L-Finistao/Portifolio/Atividades/PPRE8/mapa-mental.jpg

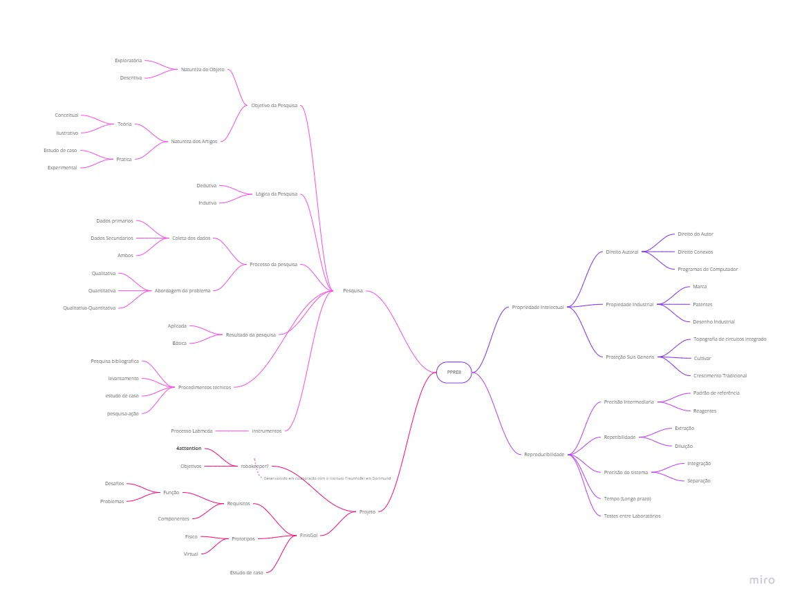
Atividades/PPRE8/mapa-mental.jpg
