L-Finistao/Portifolio/Atividades/PPRE8/Requisitos e Diagramas de Classe UML/Diagrama de Atividade.png

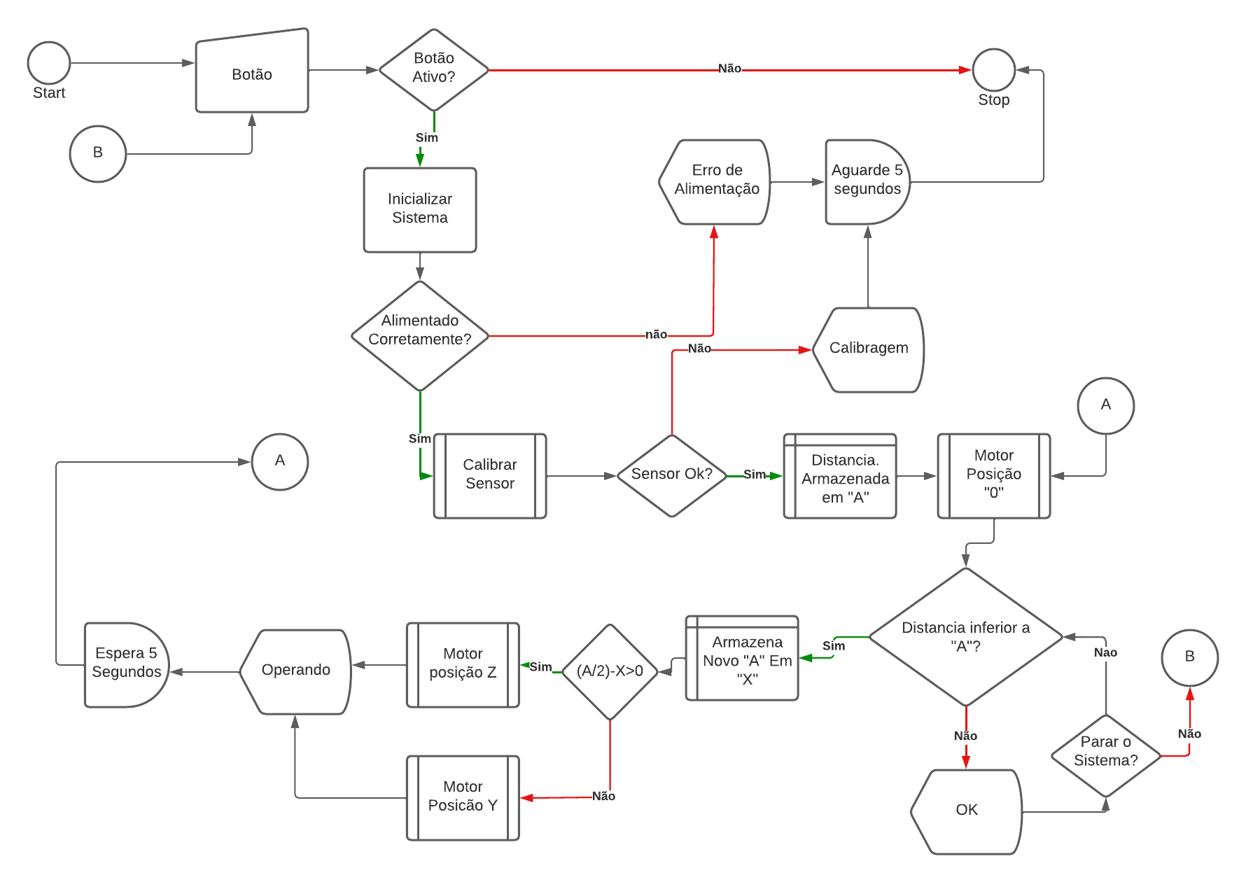
Atividades/PPRE8/Requisitos e Diagramas de Classe UML/Diagrama de Atividade.png
