L-Finistao/Portifolio/Atividades/PPRE8/Requisitos e Diagramas de Classe UML/Diagrama de Estado.png

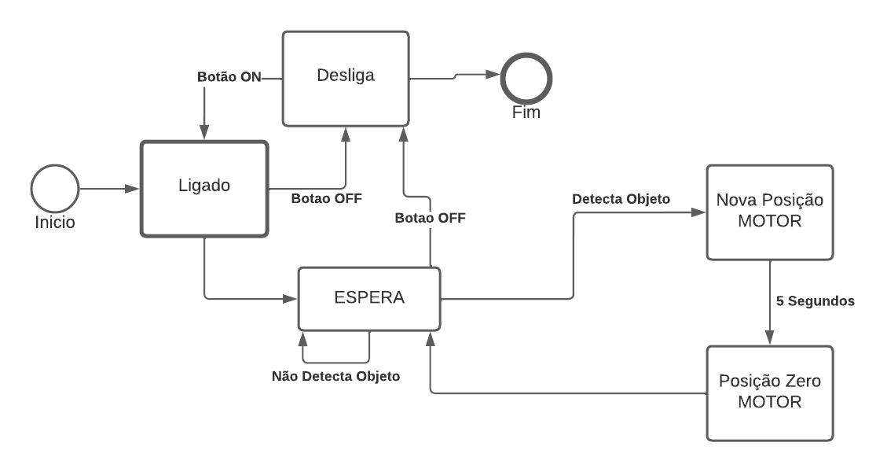
Atividades/PPRE8/Requisitos e Diagramas de Classe UML/Diagrama de Estado.png
