L-Finistao/Portifolio/Projeto/Cronograma definido.PNG

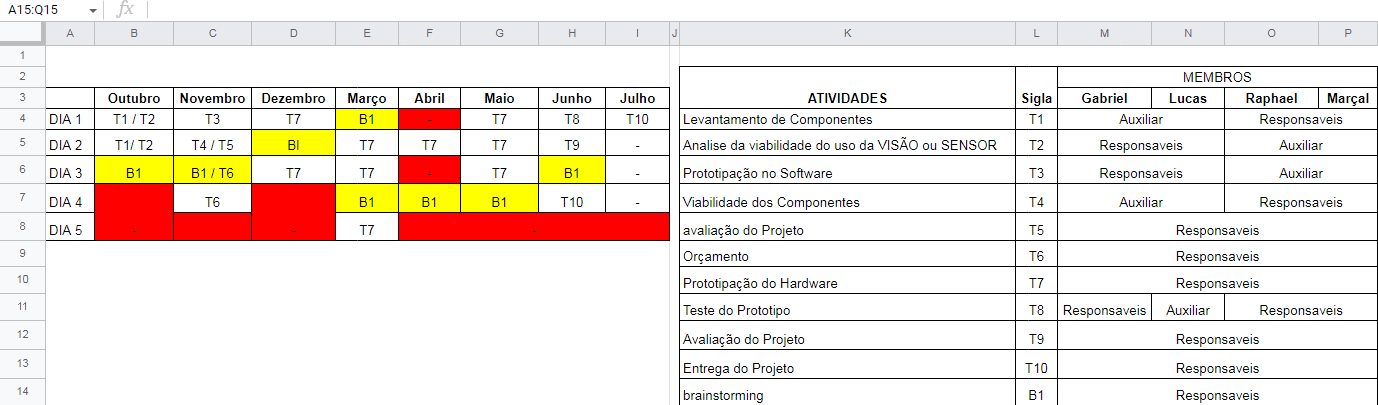
Projeto/Cronograma definido.PNG
