L-Finistao/Portifolio/Projeto/Modelo 3d & Imagens/Imagens e Medidas/Imagens Faces/Base0.jpg

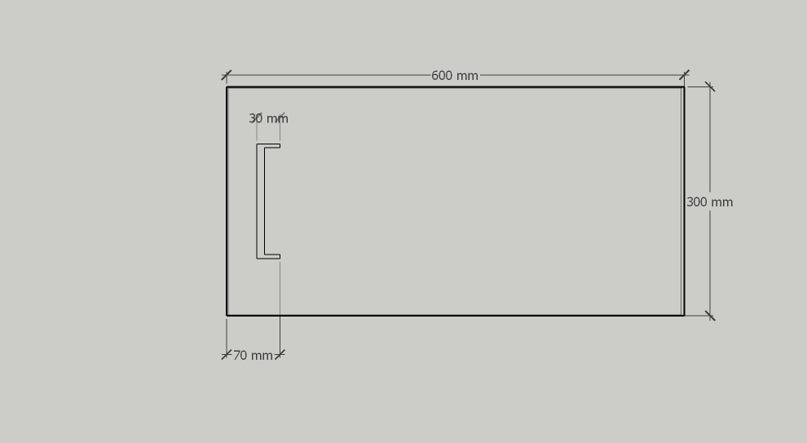
Projeto/Modelo 3d & Imagens/Imagens e Medidas/Imagens Faces/Base0.jpg
