L-Finistao/Portifolio/Projeto/Modelo 3d & Imagens/Imagens e Medidas/Imagens Faces/Eixo.jpg

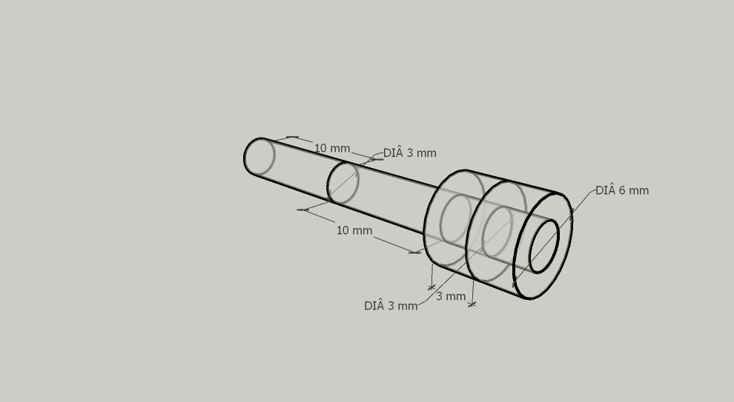
Projeto/Modelo 3d & Imagens/Imagens e Medidas/Imagens Faces/Eixo.jpg
