L-Finistao/Portifolio/Projeto/Modelo 3d & Imagens/Imagens e Medidas/Imagens Faces/Gol.jpg

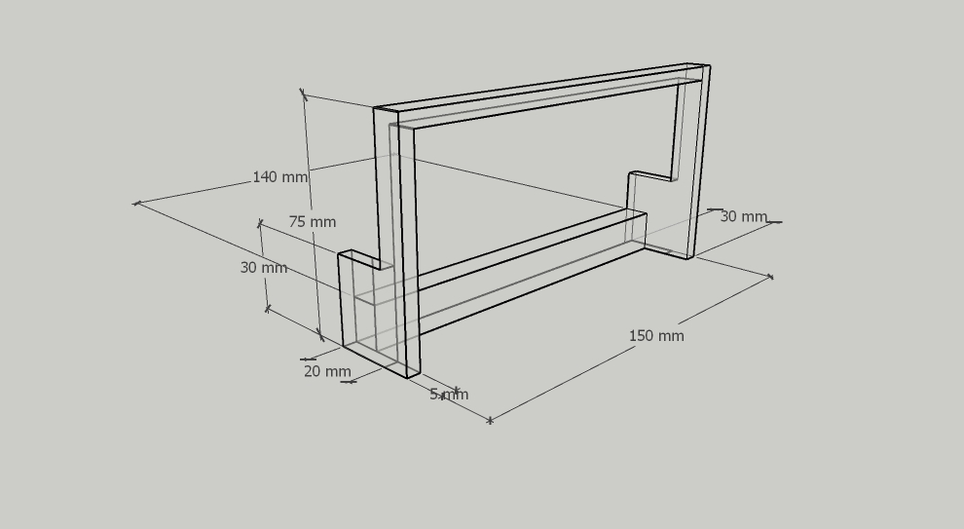
Projeto/Modelo 3d & Imagens/Imagens e Medidas/Imagens Faces/Gol.jpg
