L-Finistao/Portifolio/Projeto/Modelo 3d & Imagens/Imagens e Medidas/Imagens Faces/Suporte1.jpg

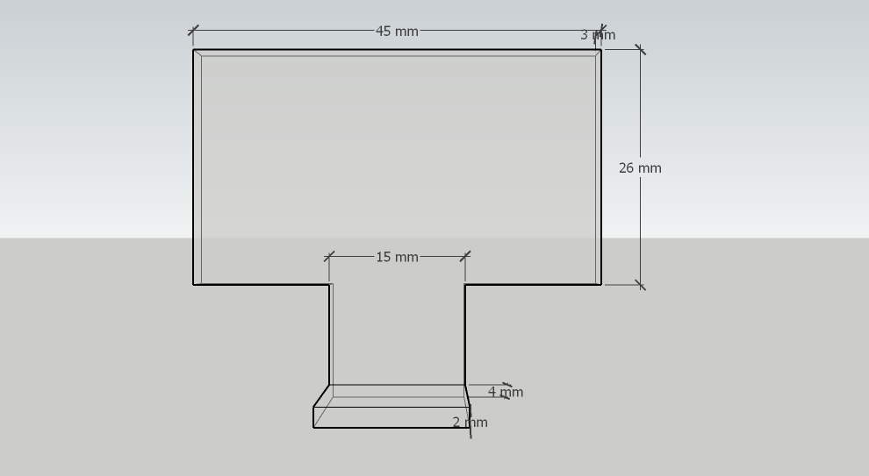
Projeto/Modelo 3d & Imagens/Imagens e Medidas/Imagens Faces/Suporte1.jpg
