L-Finistao/Portifolio/Projeto/Modelo 3d & Imagens/Imagens e Medidas/Imagens Faces/SuporteLed.jpg

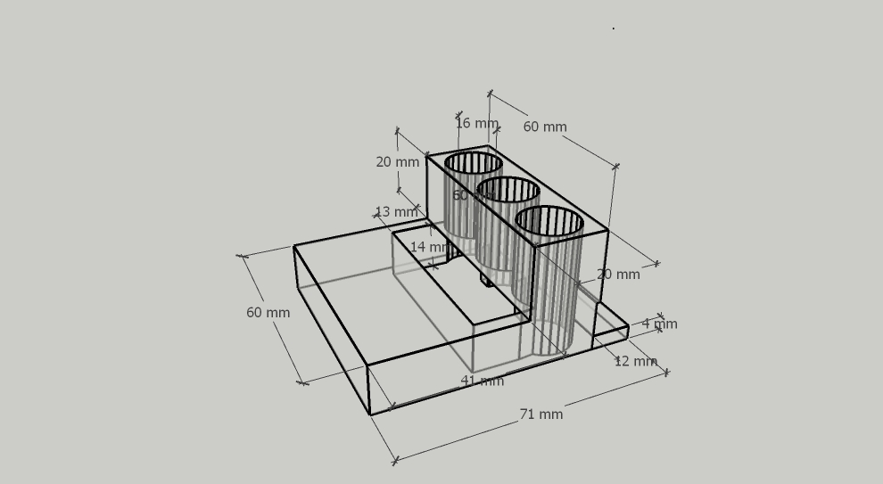
Projeto/Modelo 3d & Imagens/Imagens e Medidas/Imagens Faces/SuporteLed.jpg
