L-Finistao/Portifolio/Projeto/Modelo 3d & Imagens/Imagens e Medidas/Imagens Faces/SuporteMotor.jpg

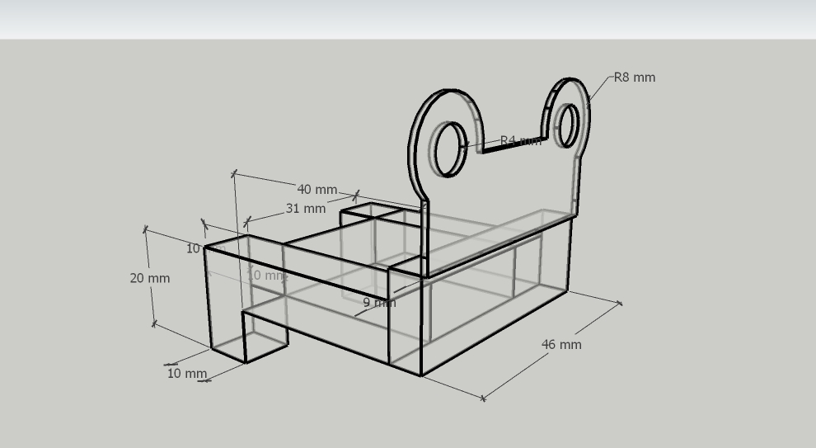
Projeto/Modelo 3d & Imagens/Imagens e Medidas/Imagens Faces/SuporteMotor.jpg
