L-Finistao/Portifolio/Projeto/Modelo 3d & Imagens/Imagens e Medidas/Imagens Geral/1.jpg

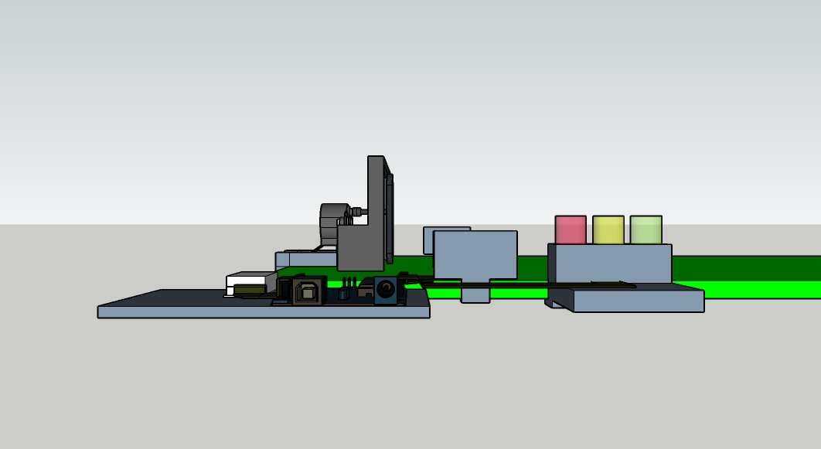
Projeto/Modelo 3d & Imagens/Imagens e Medidas/Imagens Geral/1.jpg
