L-Finistao/Portifolio/Projeto/Modelo 3d & Imagens/Imagens e Medidas/Imagens Geral/3.jpg

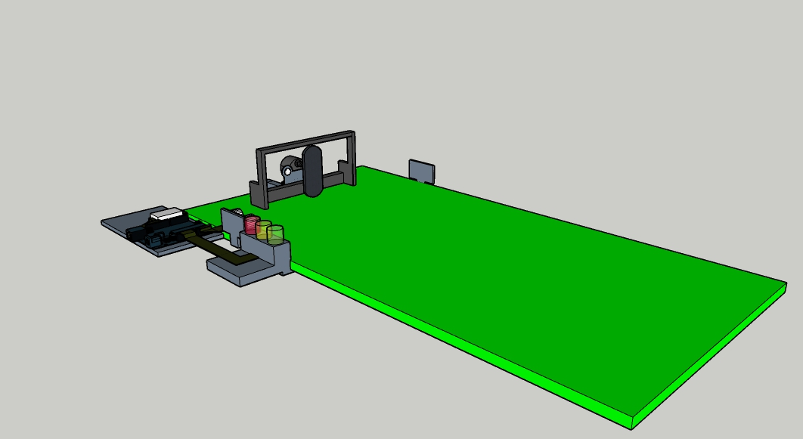
Projeto/Modelo 3d & Imagens/Imagens e Medidas/Imagens Geral/3.jpg
