L-Finistao/Portifolio/Projeto/Projeto_Modelo_Simples_3d.jpg

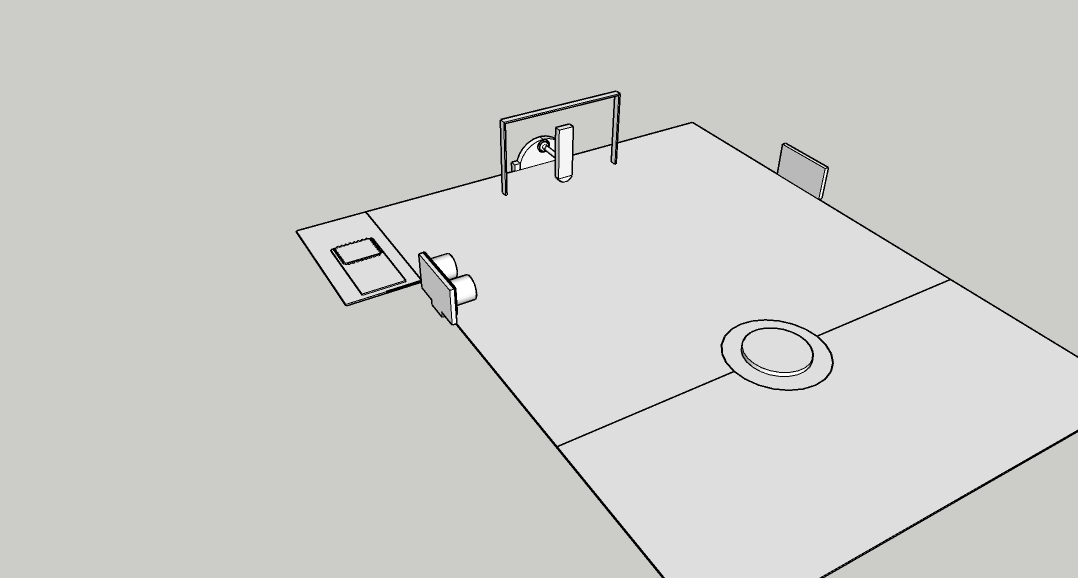
Projeto/Projeto_Modelo_Simples_3d.jpg
