L-Finistao/Portifolio/Projeto/Fotos da montagem/impressão feitas/impressão 01.jpg

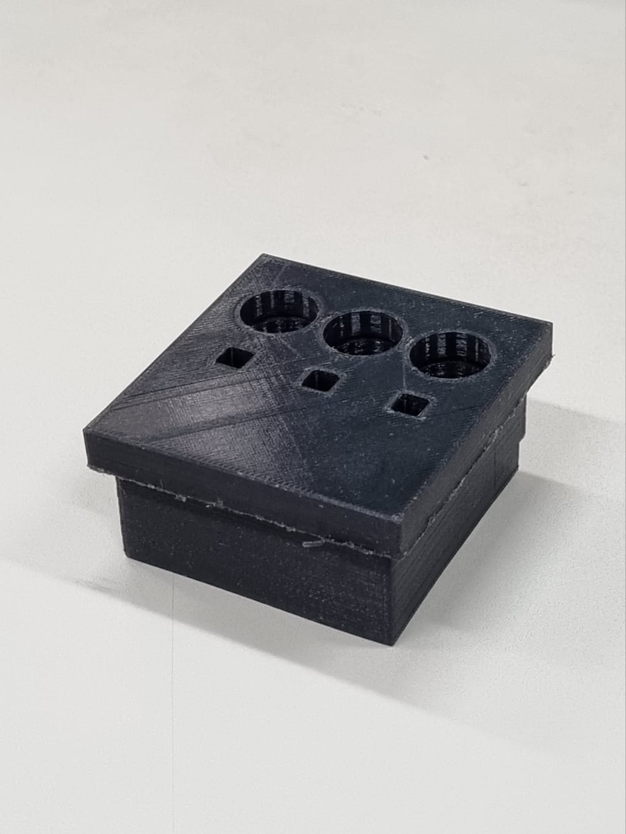
Projeto/Fotos da montagem/impressão feitas/impressão 01.jpg
