L-Finistao/Portifolio/Projeto/Fotos da montagem/impressão feitas/impressão 02.jpg

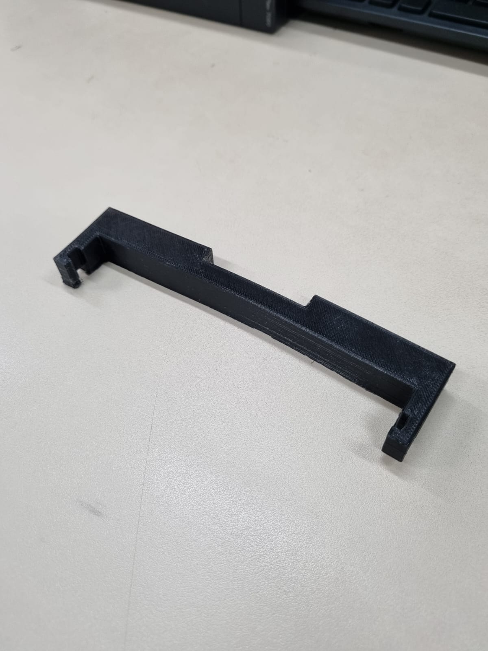
Projeto/Fotos da montagem/impressão feitas/impressão 02.jpg
