L-Finistao/Portifolio/Projeto/Fotos da montagem/impressão feitas/impressão 03.jpg

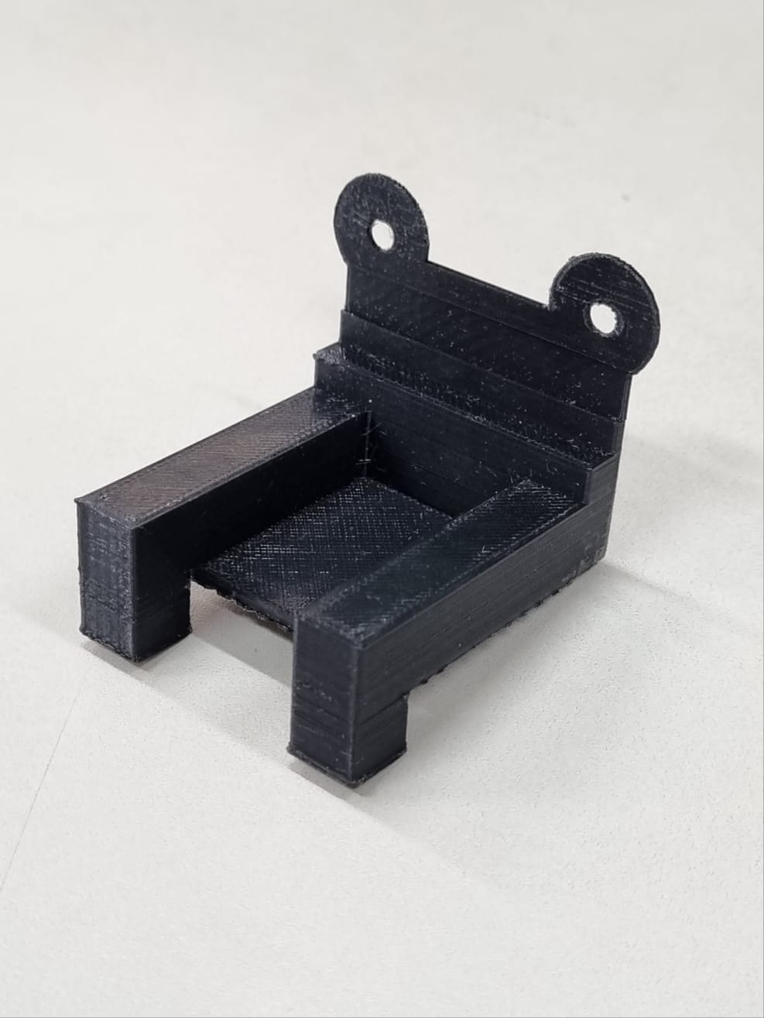
Projeto/Fotos da montagem/impressão feitas/impressão 03.jpg
