L-Finistao/Portifolio/Projeto/Fotos da montagem/impressão feitas/impressão 04.jpg

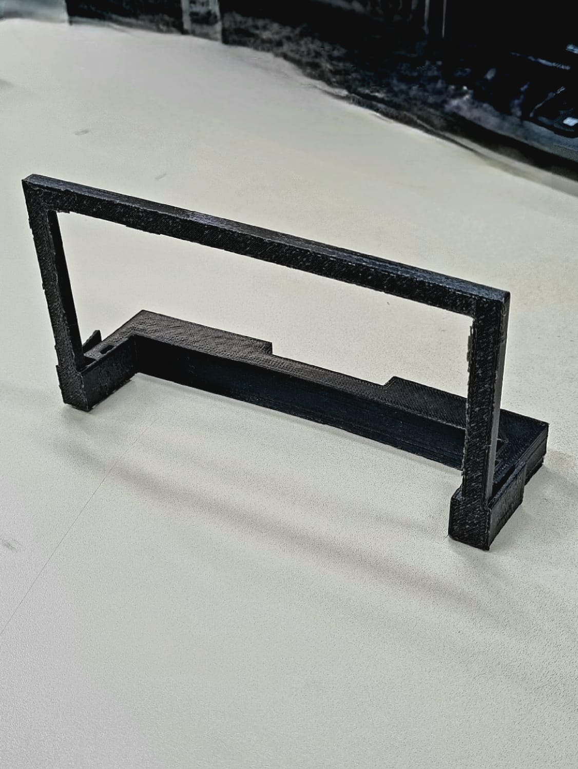
Projeto/Fotos da montagem/impressão feitas/impressão 04.jpg
