L-Finistao/Portifolio/Projeto/Fotos da montagem/impressão feitas/impressão 06.jpg

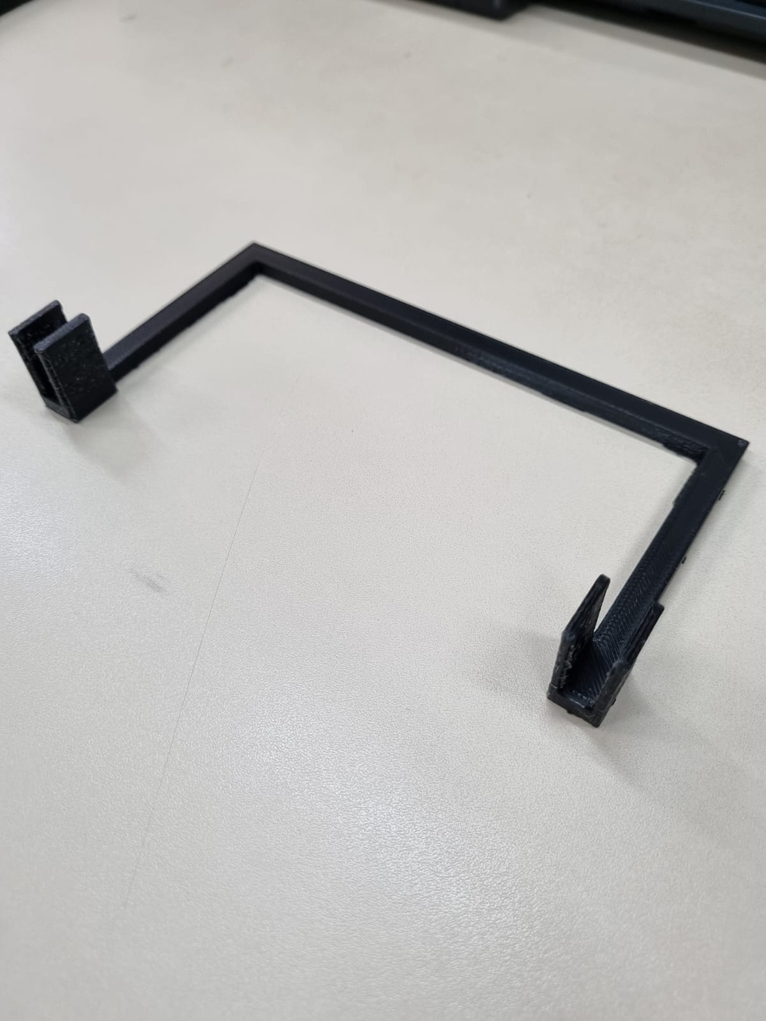
Projeto/Fotos da montagem/impressão feitas/impressão 06.jpg
