L-Finistao/Portifolio/Projeto/Fotos da montagem/impressão feitas/impressão 07.jpg

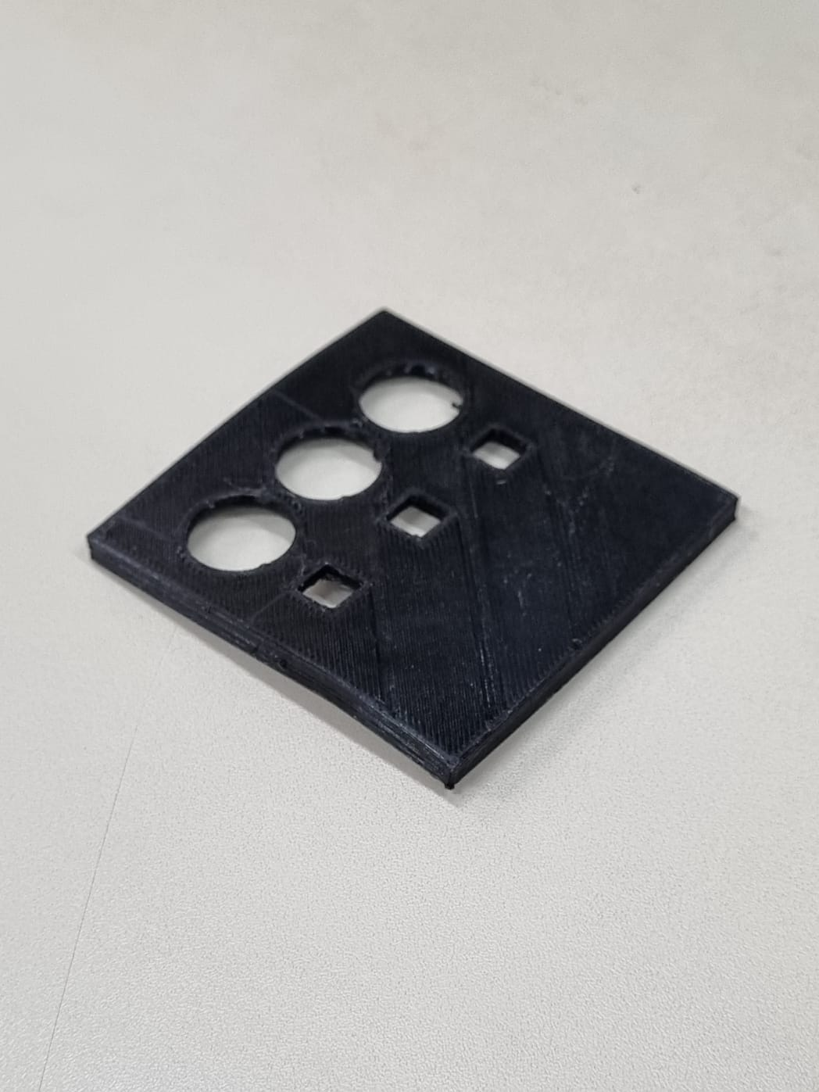
Projeto/Fotos da montagem/impressão feitas/impressão 07.jpg
