L-Finistao/Portifolio/Projeto/Fotos da montagem/Montagem do circuito/circuito no simulador.png

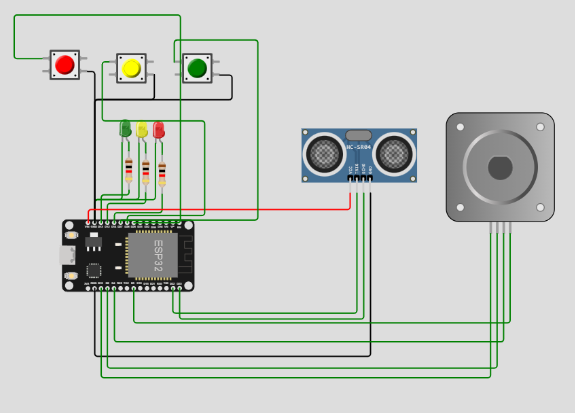
Projeto/Fotos da montagem/Montagem do circuito/circuito no simulador.png
