L-Finistao/Portifolio/Projeto/Fotos da montagem/Processo de impressão/Ajustes nas peças impressas.jpg

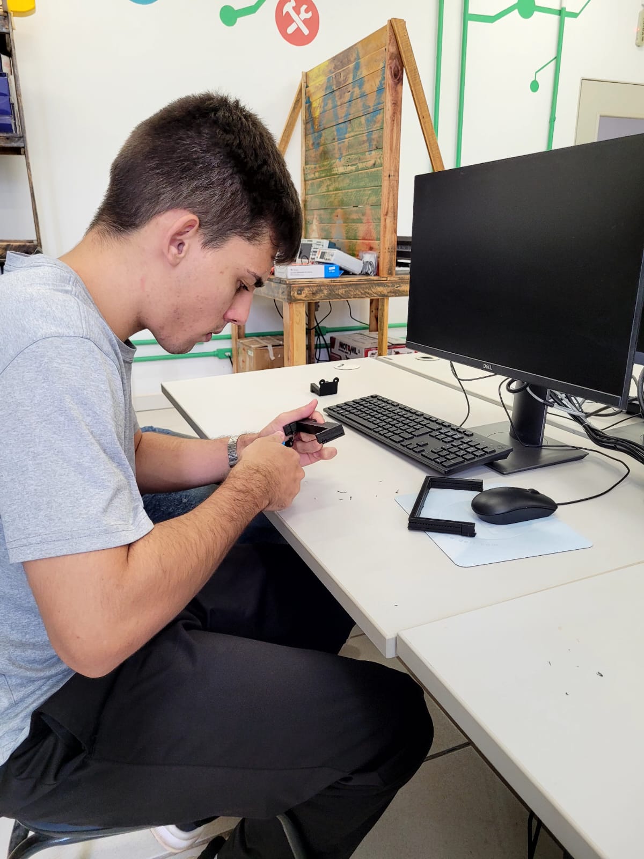
Projeto/Fotos da montagem/Processo de impressão/Ajustes nas peças impressas.jpg
