L-Finistao/Portifolio/Projeto/Fotos da montagem/Processo de impressão/impressão 03.jpg

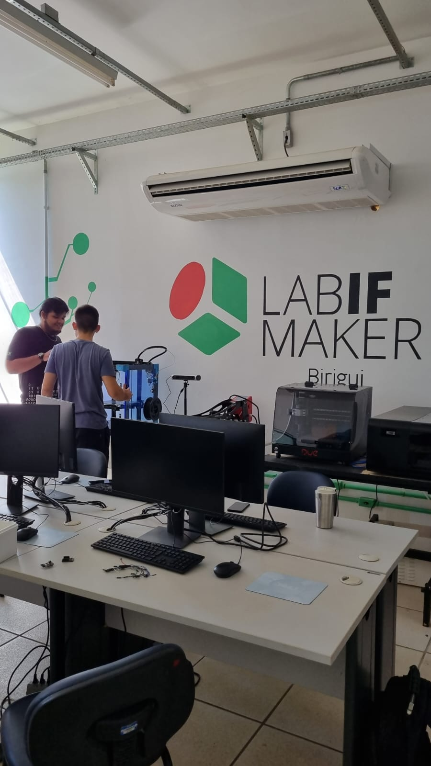
Projeto/Fotos da montagem/Processo de impressão/impressão 03.jpg
