L-Finistao/Portifolio/Projeto/Fotos da montagem/Processo de impressão/impressão 04.jpg

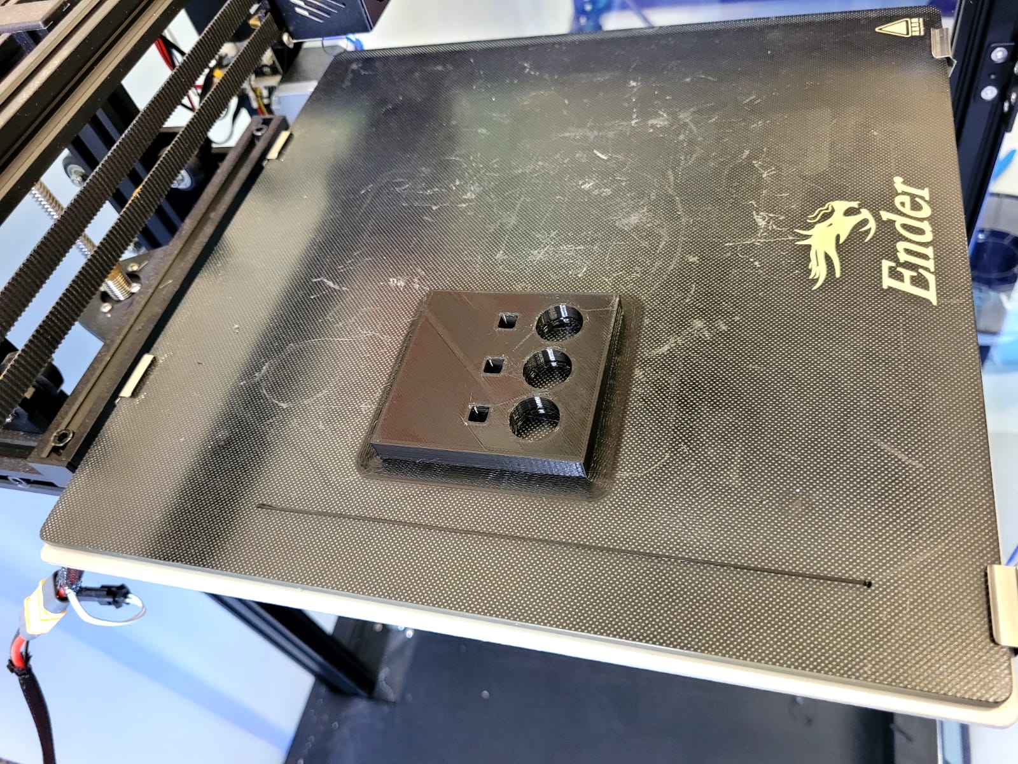
Projeto/Fotos da montagem/Processo de impressão/impressão 04.jpg
