L-Finistao/Portifolio/Projeto/Fotos da montagem/Processo de impressão/impressão 05.jpg

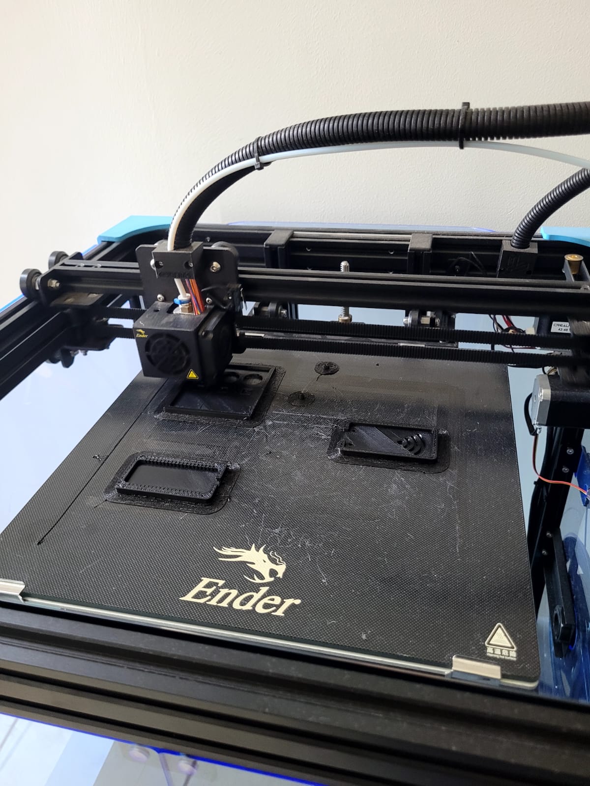
Projeto/Fotos da montagem/Processo de impressão/impressão 05.jpg
