L-Finistao/Portifolio/Projeto/Fotos da montagem/Processo de impressão/impressão 06.jpg

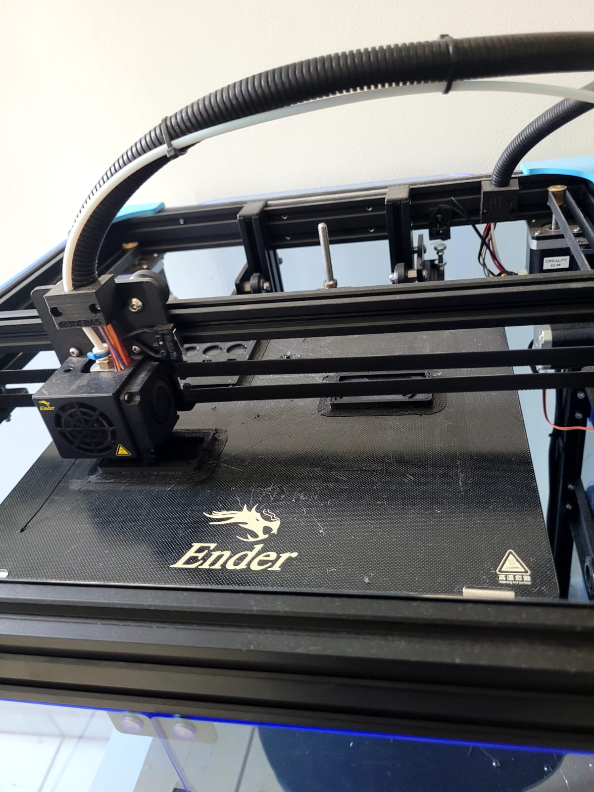
Projeto/Fotos da montagem/Processo de impressão/impressão 06.jpg
