L-Finistao/Portifolio/Projeto/Fotos da montagem/Processo de impressão/impressão 07.jpg

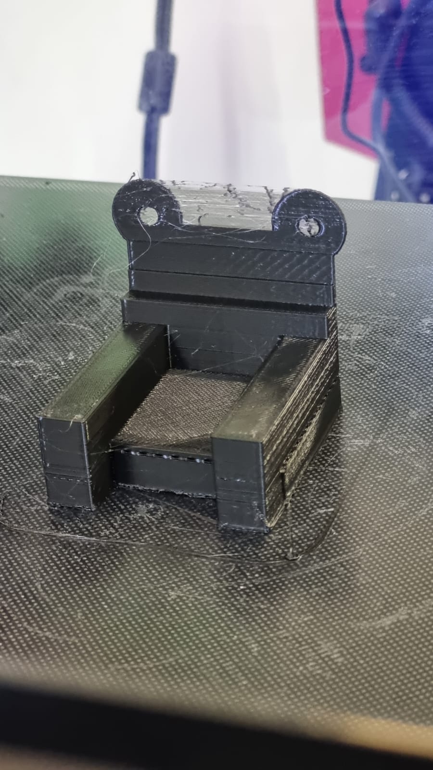
Projeto/Fotos da montagem/Processo de impressão/impressão 07.jpg
