L-Finistao/Portifolio/Projeto/Fotos da montagem/Processo de impressão/impressão 09.jpg

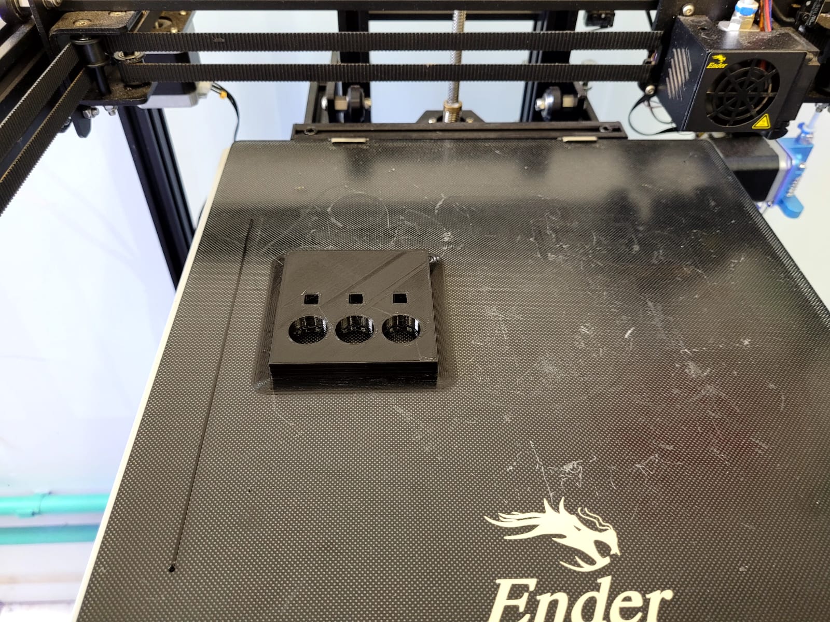
Projeto/Fotos da montagem/Processo de impressão/impressão 09.jpg
