L-Finistao/Portifolio/Projeto/Fotos da montagem/Processo de impressão/impressão 11.jpg

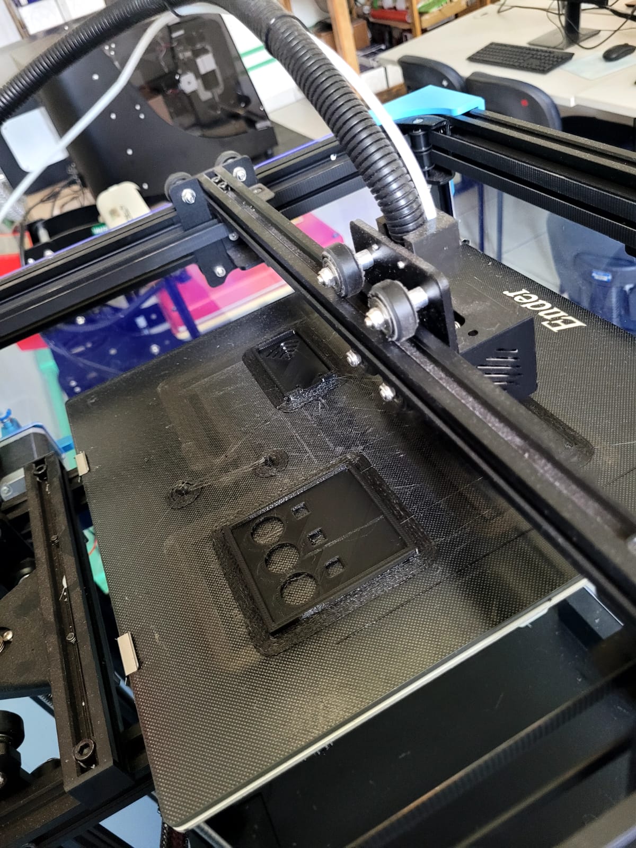
Projeto/Fotos da montagem/Processo de impressão/impressão 11.jpg
