L-Finistao/Portifolio/Projeto/Fotos da montagem/Prototipo 1.jpg

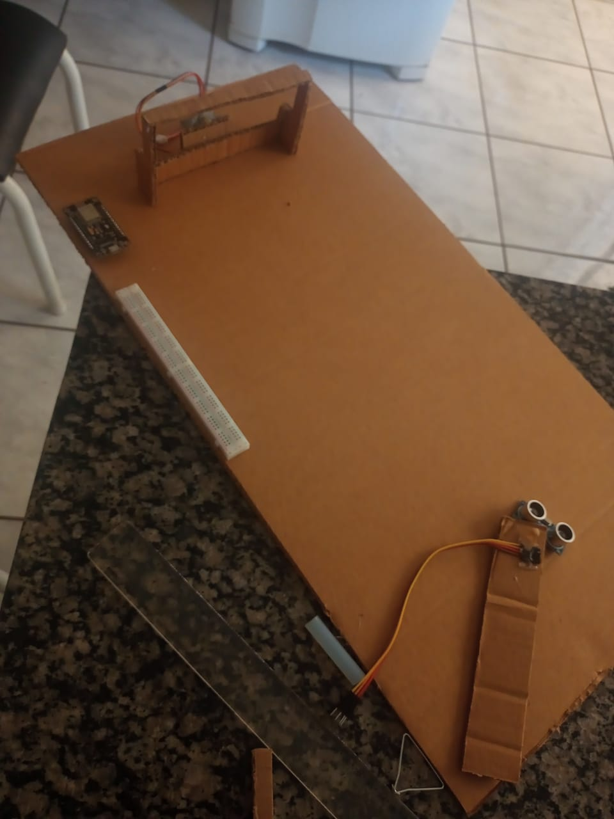
Projeto/Fotos da montagem/Prototipo 1.jpg
