L-Finistao/Portifolio/Projeto/Fotos da montagem/Montagem do circuito/Testes no circuito.jpg

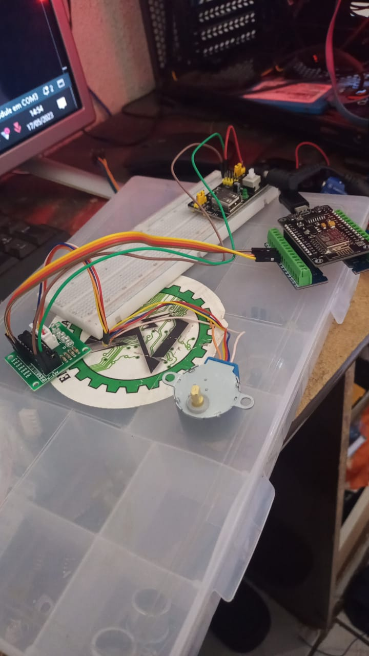
Projeto/Fotos da montagem/Montagem do circuito/Testes no circuito.jpg
