L-Finistao/Portifolio/Projeto/Fotos da montagem/Processo de impressão/Problemas na impressão - impressora.jpg

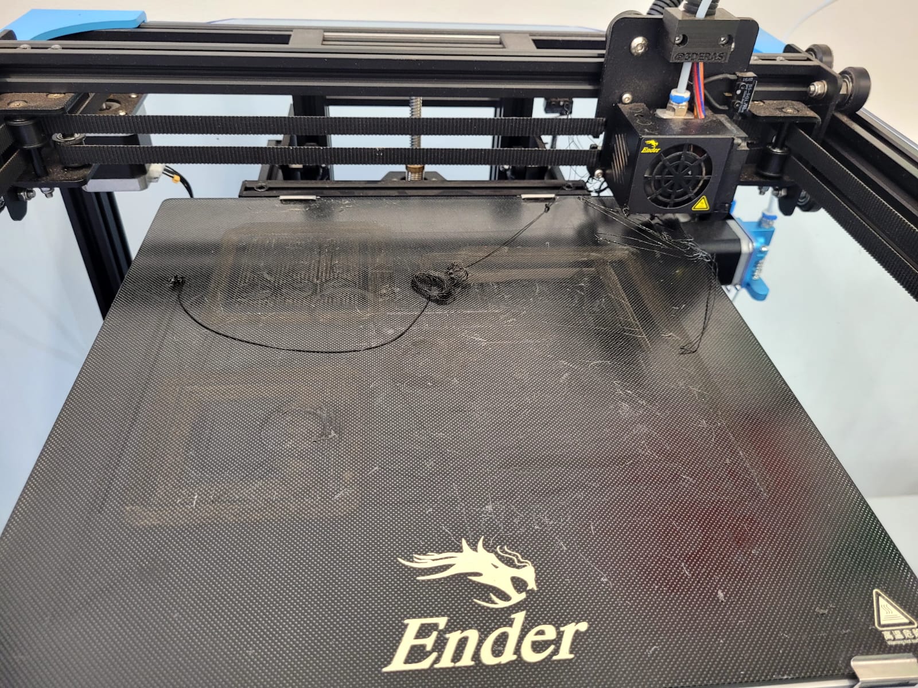
Projeto/Fotos da montagem/Processo de impressão/Problemas na impressão - impressora.jpg
