L-Finistao/Portifolio/Projeto/Fotos da montagem/Processo de impressão/Problemas na impressão - Solução.jpg

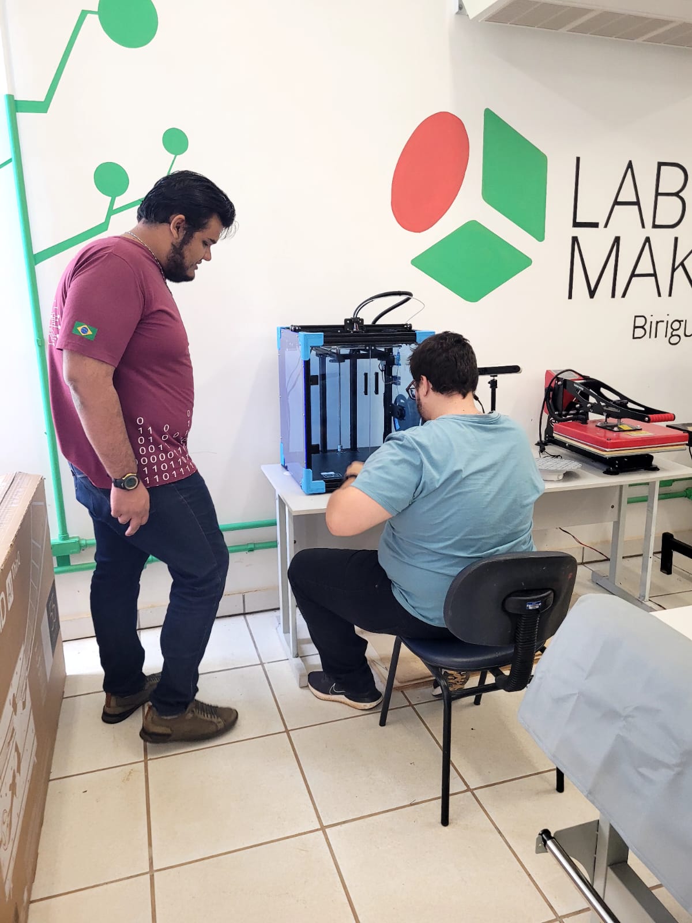
Projeto/Fotos da montagem/Processo de impressão/Problemas na impressão - Solução.jpg
